akuker/adbuino/src/adbuino/src/usbmouseparser.cpp

//---------------------------------------------------------------------------
//
//	ADBuino ADB keyboard and mouse adapter
//
//	   Copyright (C) 2021-2022 akuker
//
//  This file is part of ADBuino.
//
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
#include "usbinterface.h"
extern bool global_debug;

bool MouseRptParser::MouseChanged()
{
    return ((m_movedx != 0) || (m_movedy != 0) || m_mouse_button_changed);
}
int32_t MouseRptParser::GetDeltaX()
{
    return m_movedx;
}
int32_t MouseRptParser::GetDeltaY()
{
    return m_movedy;
}
void MouseRptParser::ResetMouseMovement()
{
    m_movedy = 0;
    m_movedx = 0;
    m_mouse_button_changed = false;
}
bool MouseRptParser::MouseButtonIsPressed()
{
    return m_mouse_button_is_pressed;
}

uint32_t MouseRptParser::EightBitToSevenBitSigned(int8_t value)
{
    // Dividing the value by 2 has 2 benefits:
    //   - Easy way to convert from 8 bit to 7 bit number
    //   - It "softens" the mouse movement. Modern optical
    //     mice seem a little jumpy.
    return (uint32_t)((value/2) & 0x7F);
}

uint16_t MouseRptParser::GetAdbRegister0()
{
    uint16_t reg_value = 0;
    // Bit 15 = Button Status; 0=down
    if (!MouseButtonIsPressed())
    {
        reg_value |= (1 << 15);
    }
    // Bit 7 = Not used. Always 1
    reg_value |= (1 << 7);
    // Bits 14-8 = Y move Counts (Two's compliment. Negative = up, positive = down)
    reg_value |= (EightBitToSevenBitSigned(GetDeltaY()) << 8);

    // Bits 6-0 = X move counts (Two's compliment. Negative = left, positive = right)
    reg_value |= (EightBitToSevenBitSigned(GetDeltaX()) << 0);

    ResetMouseMovement();

    return reg_value;
}

void MouseRptParser::OnMouseMove(MOUSEINFO *mi)
{
    if (global_debug)
    {
        Serial.print("dx=");
        Serial.print(mi->dX, DEC);
        Serial.print(" dy=");
        Serial.println(mi->dY, DEC);
    }
    m_movedy = mi->dY;
    m_movedx = mi->dX;
};
void MouseRptParser::OnLeftButtonUp(MOUSEINFO *mi)
{
    if (global_debug)
    {
        Serial.println("L Butt Up");
    }
    m_mouse_button_is_pressed = false;
    m_mouse_button_changed = true;
};
void MouseRptParser::OnLeftButtonDown(MOUSEINFO *mi)
{
    if (global_debug)
    {
        Serial.println("L Butt Dn");
    }
    m_mouse_button_is_pressed = true;
    m_mouse_button_changed = true;
};
void MouseRptParser::OnRightButtonUp(MOUSEINFO *mi)
{
    if (global_debug)
    {
        Serial.println("R Butt Up");
    }
};
void MouseRptParser::OnRightButtonDown(MOUSEINFO *mi)
{
    if (global_debug)
    {
        Serial.println("R Butt Dn");
    }
};
void MouseRptParser::OnMiddleButtonUp(MOUSEINFO *mi)
{
    if (global_debug)
    {
        Serial.println("M Butt Up");
    }
};
void MouseRptParser::OnMiddleButtonDown(MOUSEINFO *mi)
{
    if (global_debug)
    {
        Serial.println("M Butt Dn");
    }
};
